ethanlefebv/S4H2021-Scarus/Mechanical_Components/ASSY_SCARUS/ASSY_ROBOT/ARM_SEGMENT_1.SLDPRT

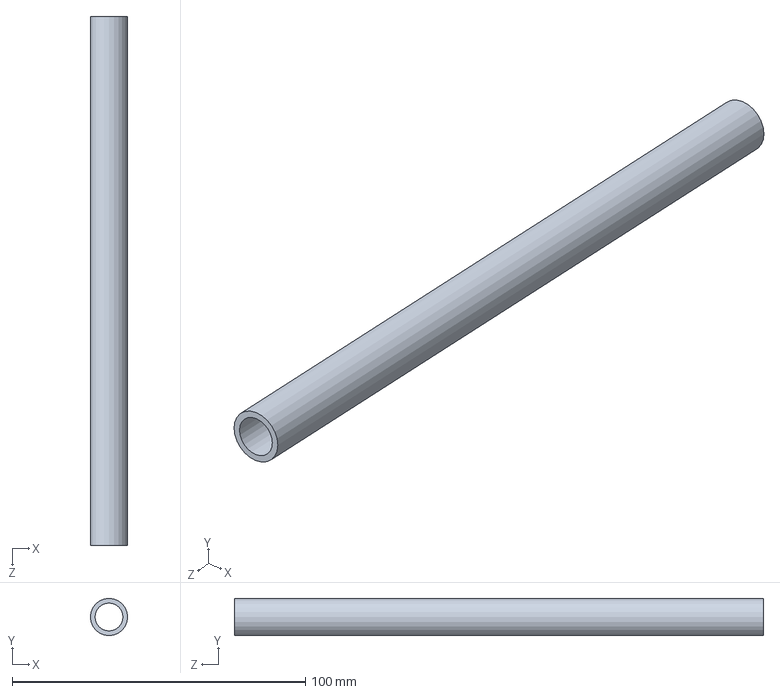
[picture p18: CAD file, 2021-04-16]
Mechanical_Components/ASSY_SCARUS/ASSY_ROBOT/ARM_SEGMENT_1.SLDPRT
12.7 x 12.7 x 180.4 mm
