ethanlefebv/S4H2021-Scarus/Mechanical_Components/ASSY_SCARUS/ASSY_ROBOT/ASSY_GRIPPER_QUICK_CONNECT/ASSY_FAN/Cooler Blades.SLDPRT

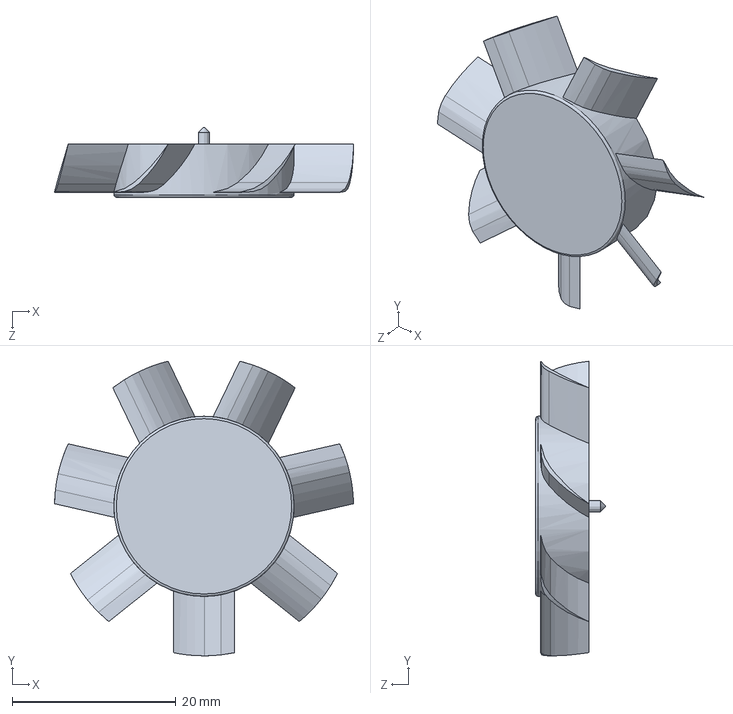
[picture p19: CAD file, 2021-04-16]
Mechanical_Components/ASSY_SCARUS/ASSY_ROBOT/ASSY_GRIPPER_QUICK_CONNECT/ASSY_FAN/Cooler Blades.SLDPRT
36.5 x 36.0 x 8.50 mm
