ethanlefebv/S4H2021-Scarus/Mechanical_Components/ASSY_SCARUS/ASSY_ROBOT/ASSY_GRIPPER_QUICK_CONNECT/ASSY_SOLENOID/SOLENOID_SLIDER.SLDPRT

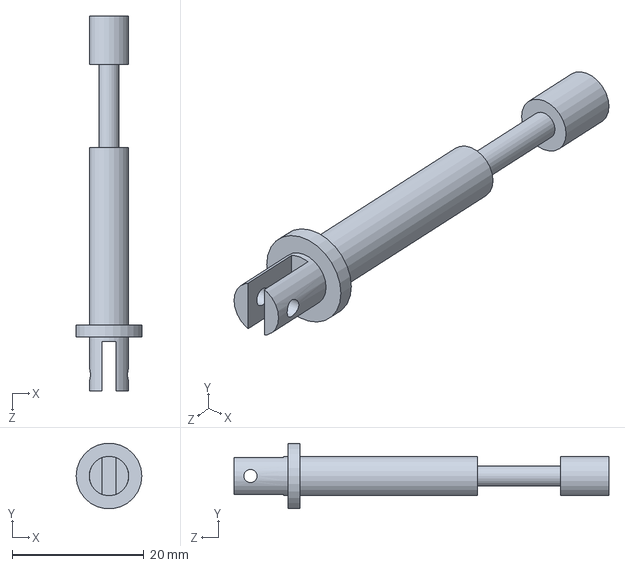
[picture p20: CAD file, 2021-04-16]
Mechanical_Components/ASSY_SCARUS/ASSY_ROBOT/ASSY_GRIPPER_QUICK_CONNECT/ASSY_SOLENOID/SOLENOID_SLIDER.SLDPRT
10.0 x 9.93 x 57.0 mm
