ethanlefebv/S4H2021-Scarus/Mechanical_Components/ASSY_SCARUS/ASSY_SLIDE/SLIDE.SLDPRT

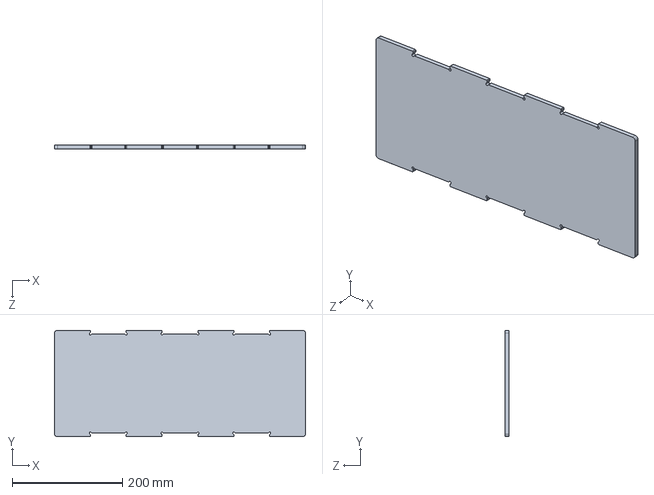
[picture p22: CAD file, 2021-04-16]
Mechanical_Components/ASSY_SCARUS/ASSY_SLIDE/SLIDE.SLDPRT
455.0 x 192.7 x 6.35 mm
