ethanlefebv/S4H2021-Scarus/Mechanical_Components/DXF/ROBOT_BASE/RBASE_BASE.DXF

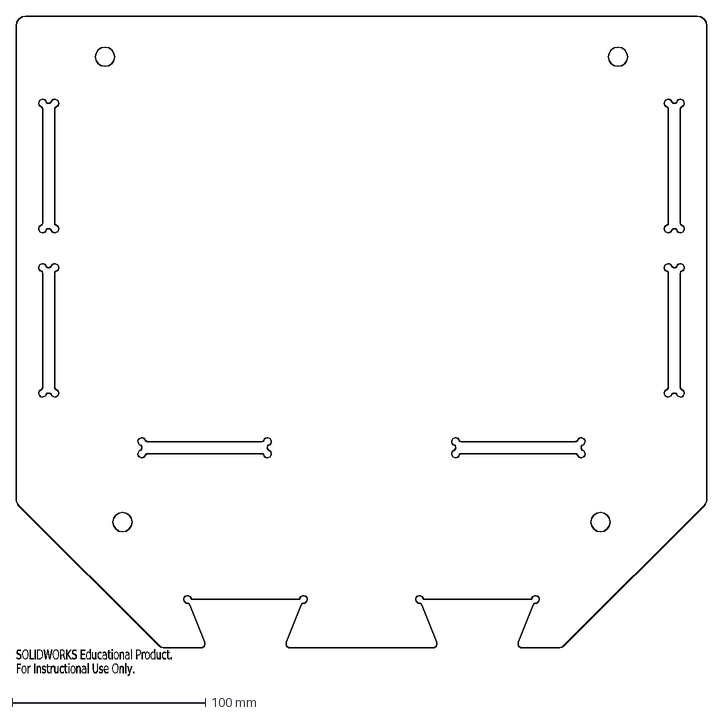
[picture p23: CAD file, 2021-04-16]
Mechanical_Components/DXF/ROBOT_BASE/RBASE_BASE.DXF
SOLIDWORKS Educational Product.
For Instructional Use Only.
