ethanlefebv/S4H2021-Scarus/Mechanical_Components/MOTOR_STAND/MOTOR_STAND_HIGH.SLDPRT

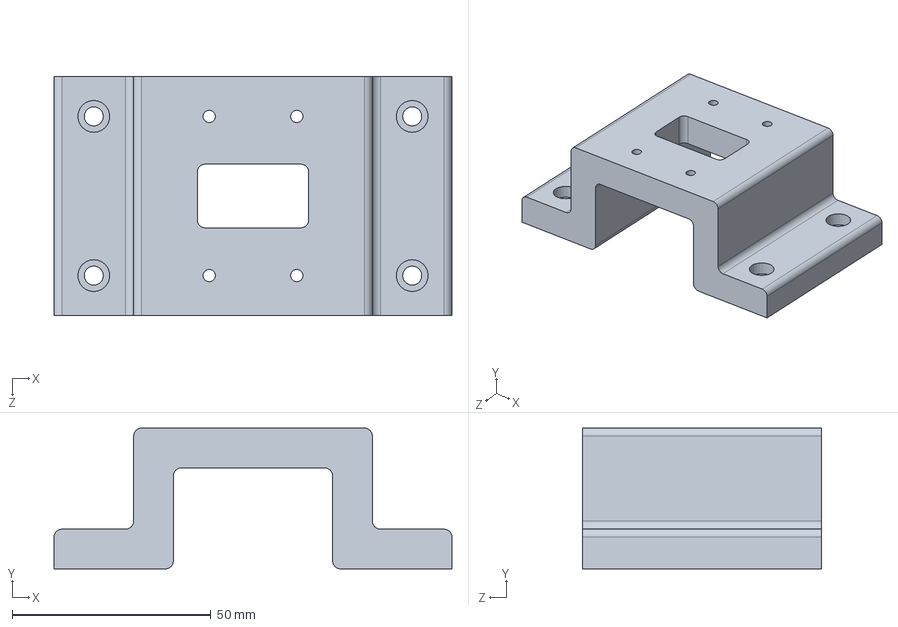
[picture p25: CAD file, 2021-04-16]
Mechanical_Components/MOTOR_STAND/MOTOR_STAND_HIGH.SLDPRT
100.0 x 35.4 x 60.0 mm
