ethanlefebv/S4H2021-Scarus/Mechanical_Components/STL/Gripper/LIFTING_SOLENOID_HOLDER.STL

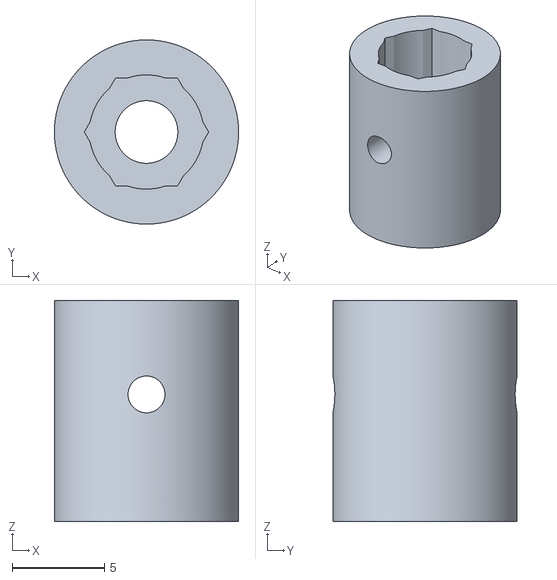
[picture p26: CAD file, 2021-04-16]
Mechanical_Components/STL/Gripper/LIFTING_SOLENOID_HOLDER.STL
10.0 x 10.0 x 12.0
