ethanlefebv/S4H2021-Scarus/Mechanical_Components/STL/PLA_BUCKET.STL

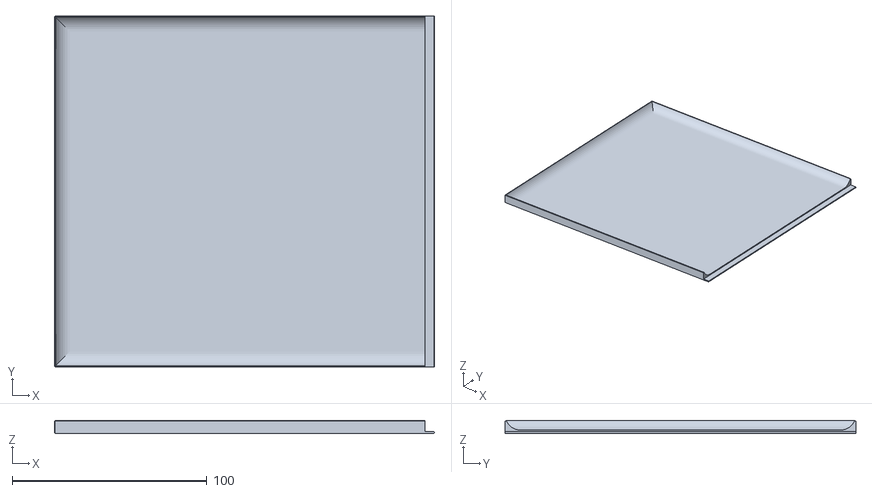
[picture p27: CAD file, 2021-02-24]
Mechanical_Components/STL/PLA_BUCKET.STL
195.0 x 180.0 x 6.42
