ethanlefebv/S4H2021-Scarus/Mechanical_Components/STL/Robot/Motors/BEARING_HOUSING.STL

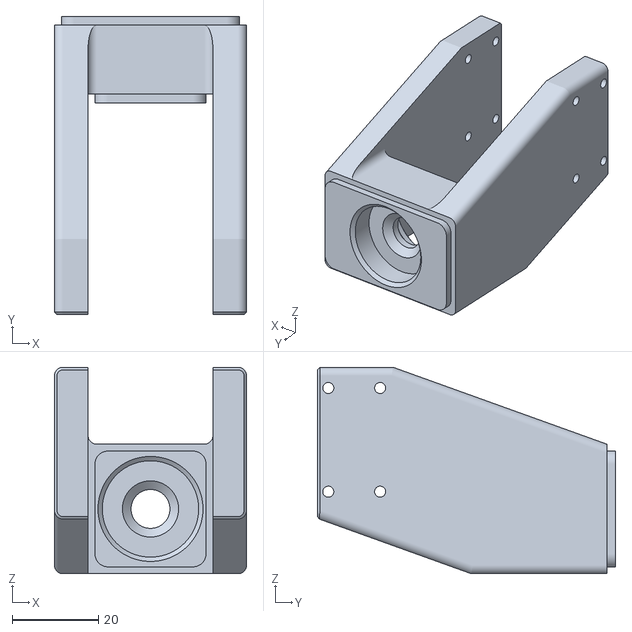
[picture p28: CAD file, 2021-04-16]
Mechanical_Components/STL/Robot/Motors/BEARING_HOUSING.STL
44.5 x 69.0 x 47.8
