ethanlefebv/S4H2021-Scarus/Mechanical_Components/ASSY_GRIPPER/SOLENOID_FIXTURE.SLDPRT

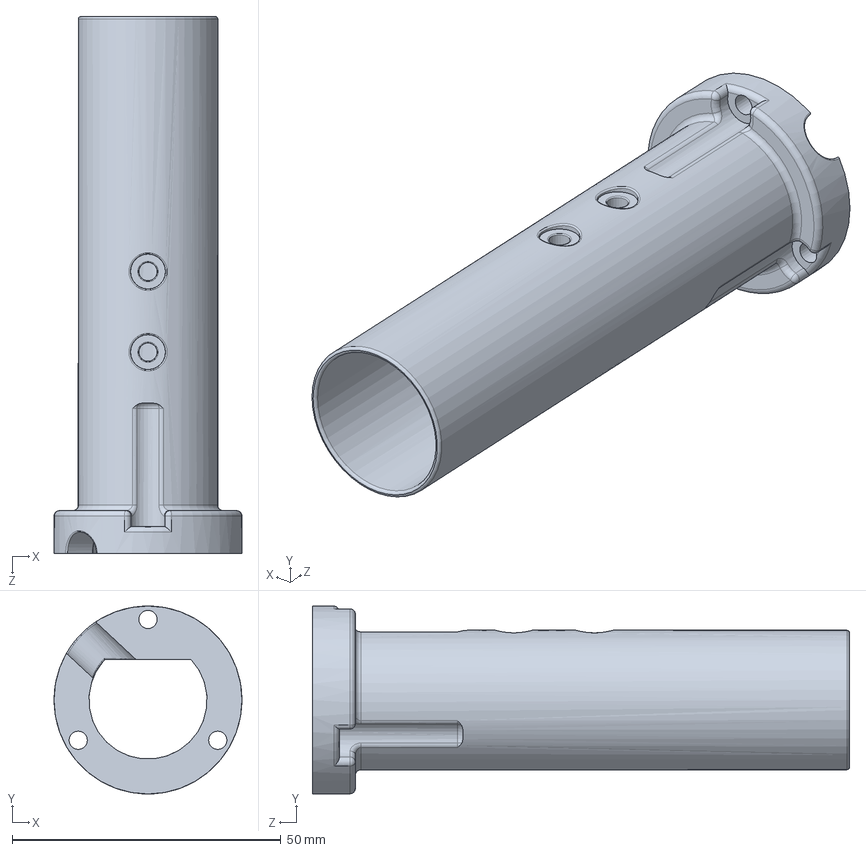
[picture p29: CAD file, 2021-04-16]
Mechanical_Components/ASSY_GRIPPER/SOLENOID_FIXTURE.SLDPRT
35.0 x 35.0 x 100.0 mm
