ethanlefebv/S4H2021-Scarus/Mechanical_Components/ASSY_SCARUS/ASSY_ROBOT/ASSY_GRIPPER_QUICK_CONNECT/ACTIONNEUR.SLDPRT

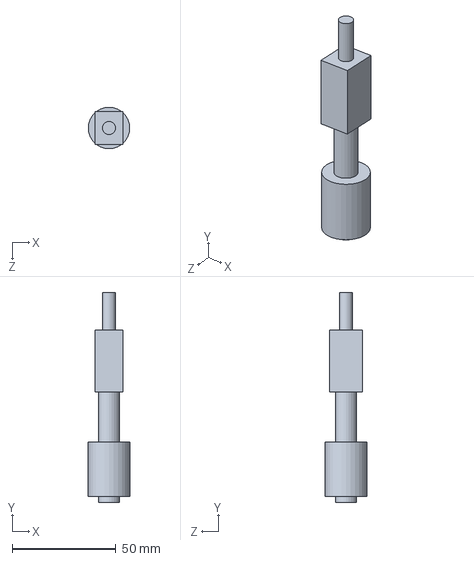
[picture p30: CAD file, 2021-04-16]
Mechanical_Components/ASSY_SCARUS/ASSY_ROBOT/ASSY_GRIPPER_QUICK_CONNECT/ACTIONNEUR.SLDPRT
20.0 x 101.2 x 20.0 mm
