ethanlefebv/S4H2021-Scarus/Mechanical_Components/ASSY_SCARUS/ASSY_ROBOT/ASSY_GRIPPER_QUICK_CONNECT/ASSY_FAN/Cooler 40x40x10 body.SLDPRT

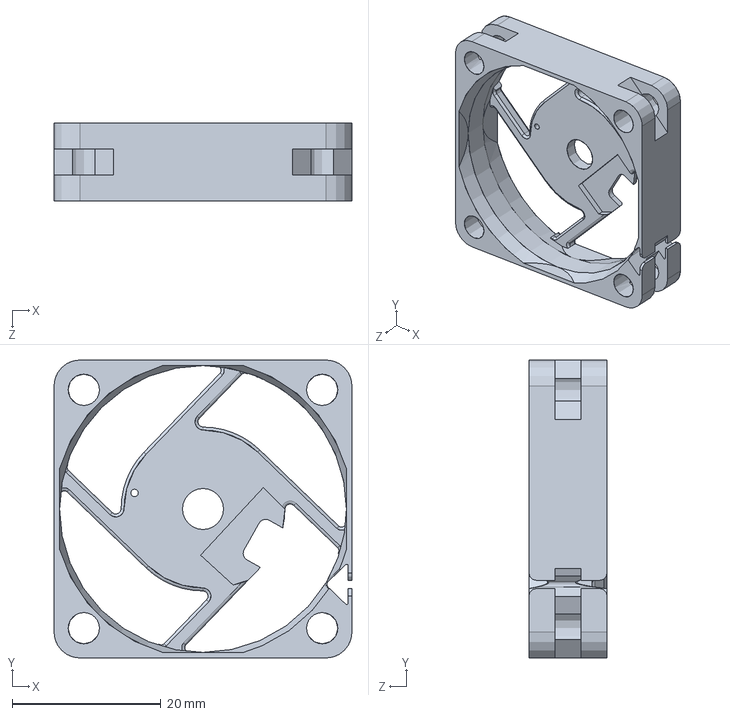
[picture p31: CAD file, 2021-04-16]
Mechanical_Components/ASSY_SCARUS/ASSY_ROBOT/ASSY_GRIPPER_QUICK_CONNECT/ASSY_FAN/Cooler 40x40x10 body.SLDPRT
40.0 x 40.0 x 10.5 mm
