ethanlefebv/S4H2021-Scarus/Mechanical_Components/ASSY_SCARUS/ASSY_ROBOT/ASSY_JOINTS/JOINT_STD.SLDPRT

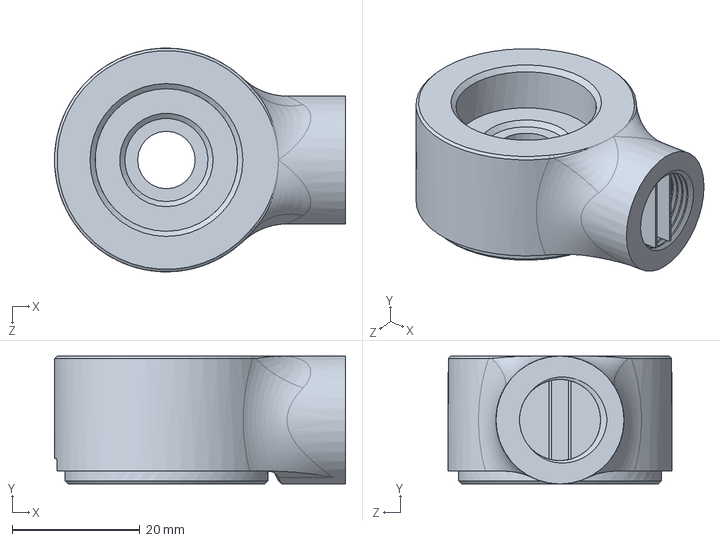
[picture p32: CAD file, 2021-04-16]
Mechanical_Components/ASSY_SCARUS/ASSY_ROBOT/ASSY_JOINTS/JOINT_STD.SLDPRT
45.5 x 20.0 x 35.0 mm
