ethanlefebv/S4H2021-Scarus/Mechanical_Components/ASSY_SCARUS/ASSY_ROBOT/BEARING_HOUSING.SLDPRT

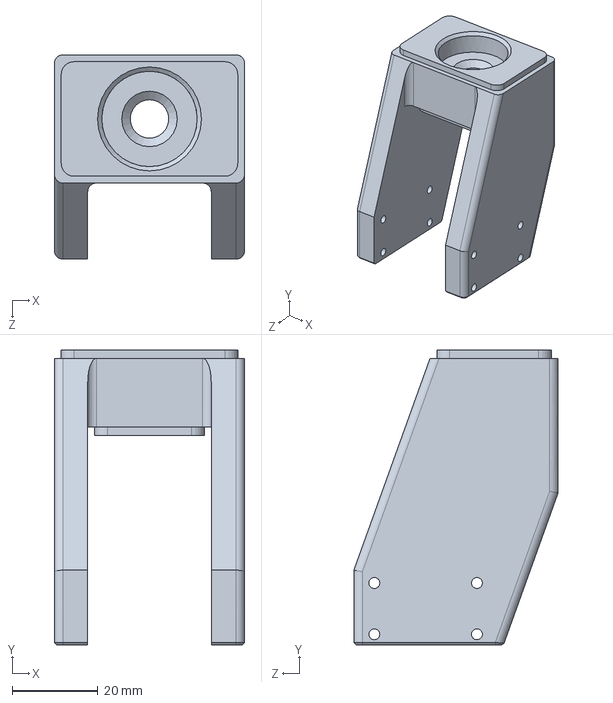
[picture p33: CAD file, 2021-04-16]
Mechanical_Components/ASSY_SCARUS/ASSY_ROBOT/BEARING_HOUSING.SLDPRT
44.5 x 69.0 x 47.8 mm
