ethanlefebv/S4H2021-Scarus/Mechanical_Components/DXF/SLIDE/SLIDE_BASE.DXF

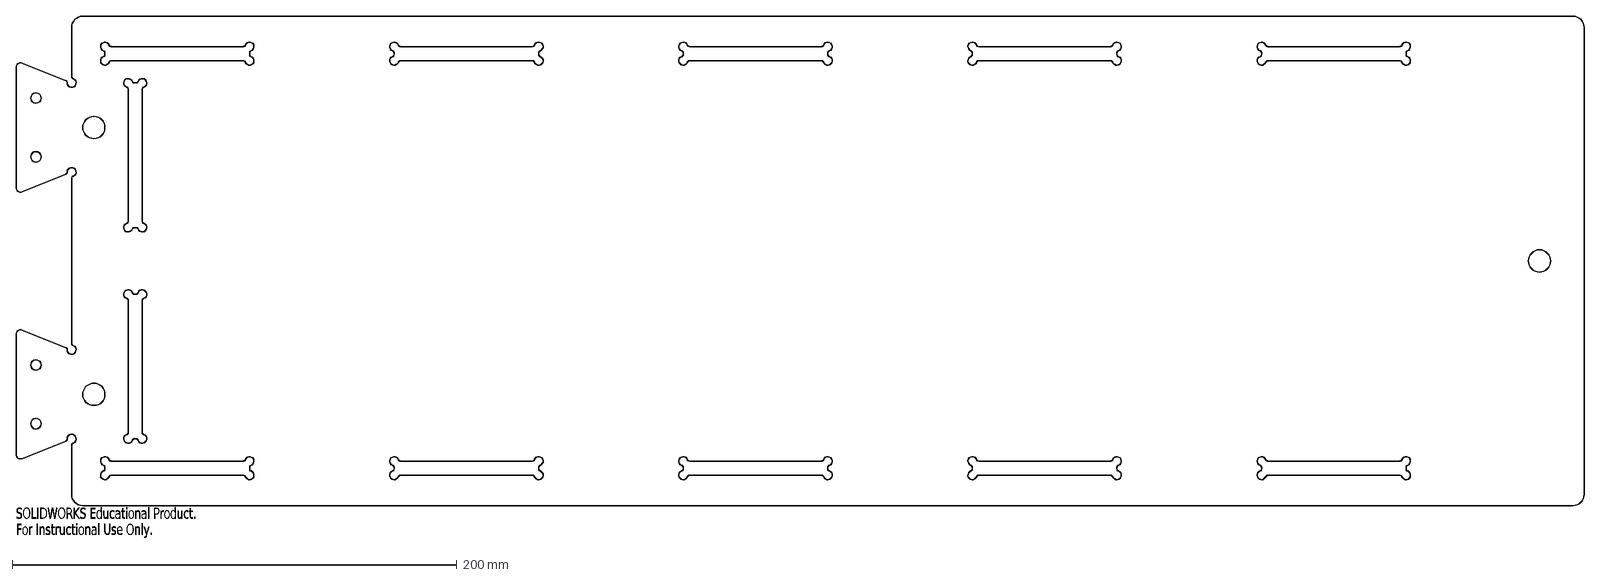
[picture p35: CAD file, 2021-04-16]
Mechanical_Components/DXF/SLIDE/SLIDE_BASE.DXF
SOLIDWORKS Educational Product.
For Instructional Use Only.
