ethanlefebv/S4H2021-Scarus/Mechanical_Components/MOTOR_STAND/MOTOR_STAND_BOT_WOOD.SLDPRT

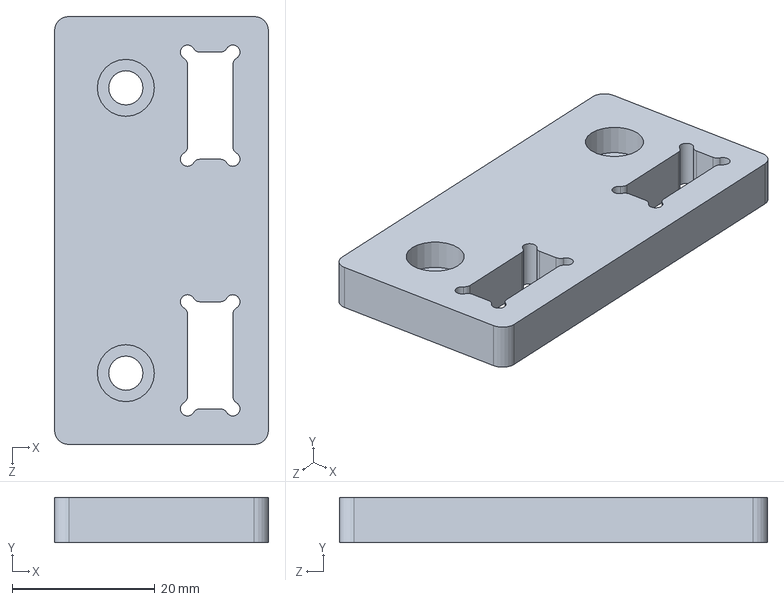
[picture p36: CAD file, 2021-04-16]
Mechanical_Components/MOTOR_STAND/MOTOR_STAND_BOT_WOOD.SLDPRT
30.0 x 6.35 x 60.0 mm
