ethanlefebv/S4H2021-Scarus/Mechanical_Components/STL/Gripper/SOLENOID_DOOR.STL

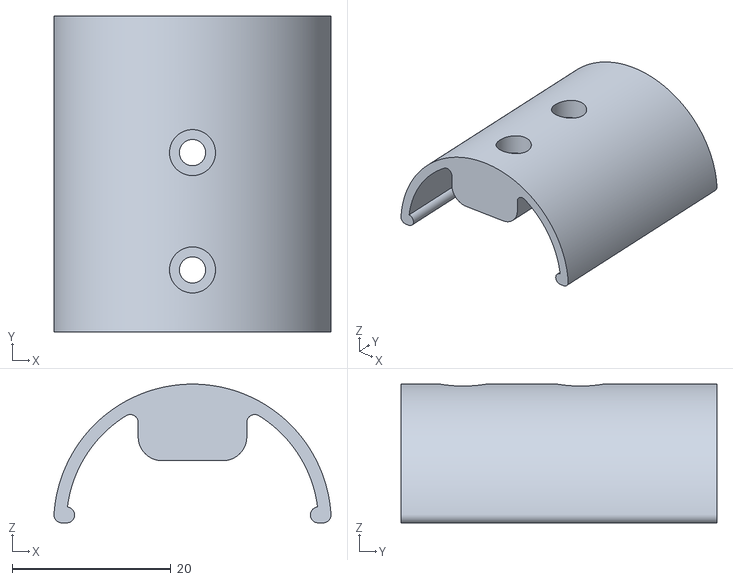
[picture p37: CAD file, 2021-04-16]
Mechanical_Components/STL/Gripper/SOLENOID_DOOR.STL
34.9 x 39.8 x 17.5
