ethanlefebv/S4H2021-Scarus/Mechanical_Components/STL/Robot/Joints/SPACER.STL

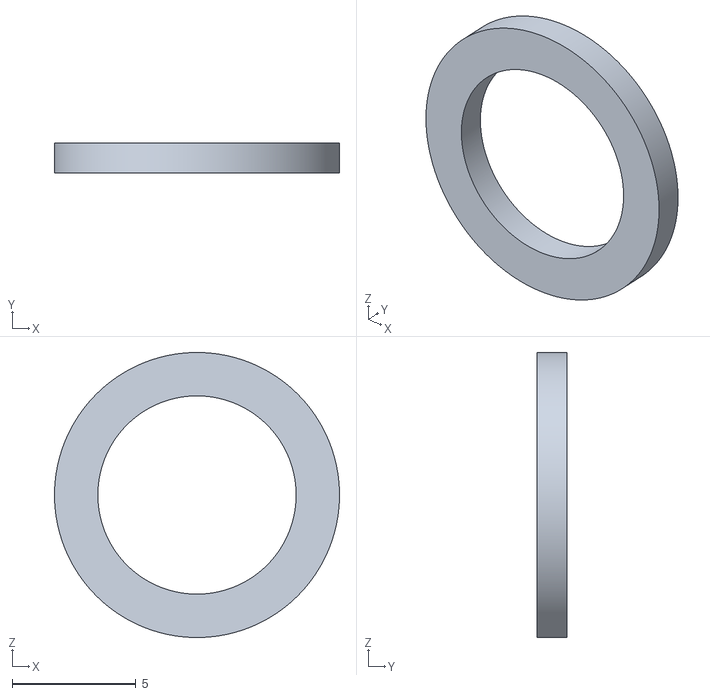
[picture p38: CAD file, 2021-04-16]
Mechanical_Components/STL/Robot/Joints/SPACER.STL
11.5 x 1.20 x 11.5
