ethanlefebv/S4H2021-Scarus/Mechanical_Components/STL/Robot/Motors/MOTOR_STAND_HIGH.STL

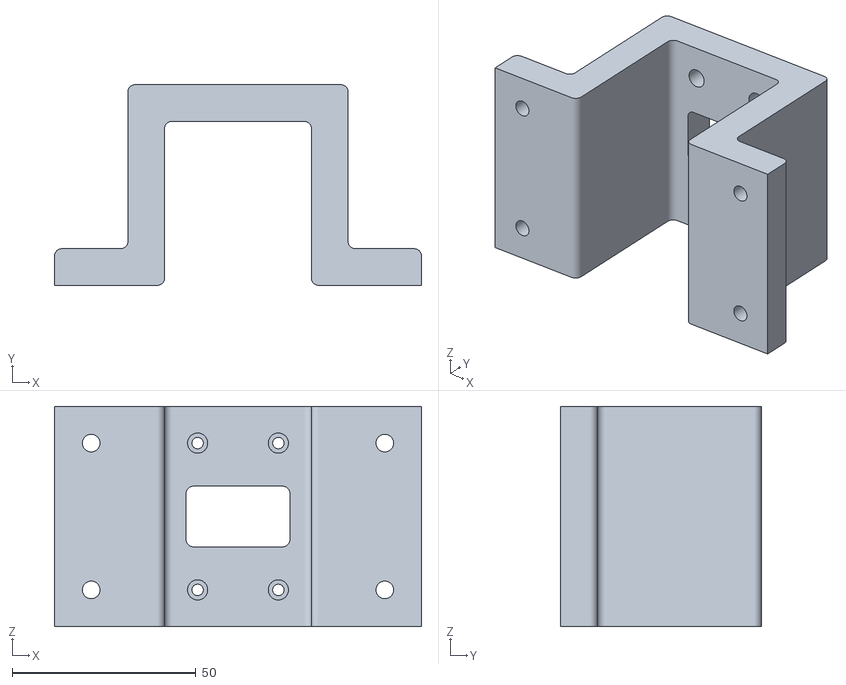
[picture p39: CAD file, 2021-04-16]
Mechanical_Components/STL/Robot/Motors/MOTOR_STAND_HIGH.STL
100.0 x 54.7 x 60.0
