ethanlefebv/S4H2021-Scarus/Mechanical_Components/ASSY_SCARUS/ASSY_ROBOT/ASSY_GRIPPER_QUICK_CONNECT/ASSY_FAN/Sticker SUNON.SLDPRT

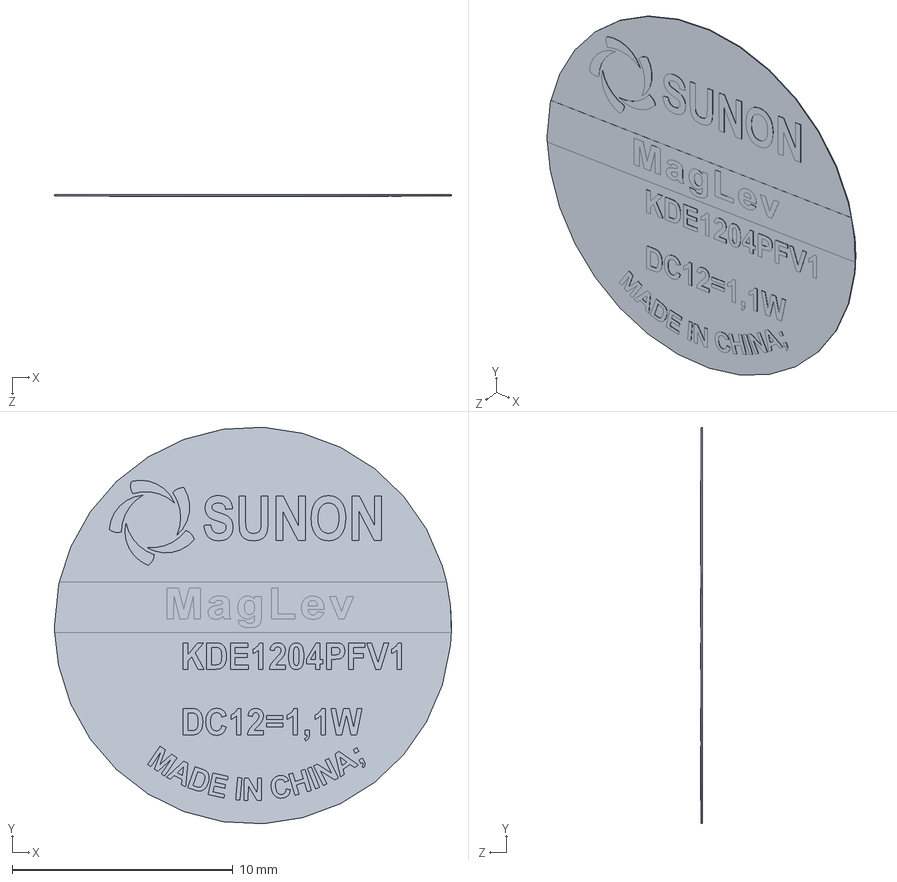
[picture p40: CAD file, 2021-04-16]
Mechanical_Components/ASSY_SCARUS/ASSY_ROBOT/ASSY_GRIPPER_QUICK_CONNECT/ASSY_FAN/Sticker SUNON.SLDPRT
18.0 x 18.0 x 0.07 mm
