ethanlefebv/S4H2021-Scarus/Mechanical_Components/ASSY_SCARUS/ASSY_ROBOT/ASSY_JOINTS/SPACER.SLDPRT

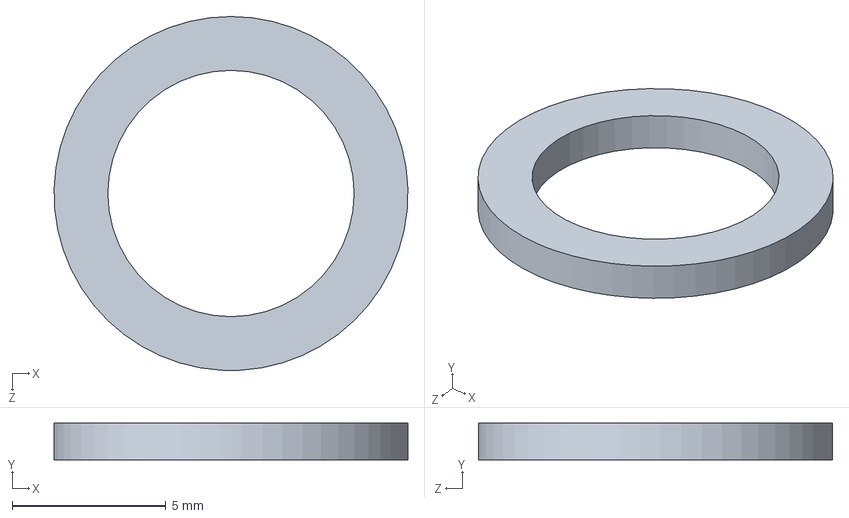
[picture p42: CAD file, 2021-04-16]
Mechanical_Components/ASSY_SCARUS/ASSY_ROBOT/ASSY_JOINTS/SPACER.SLDPRT
11.5 x 1.20 x 11.5 mm
