ethanlefebv/S4H2021-Scarus/Mechanical_Components/ASSY_SCARUS/ASSY_SLIDE/CAM.SLDPRT

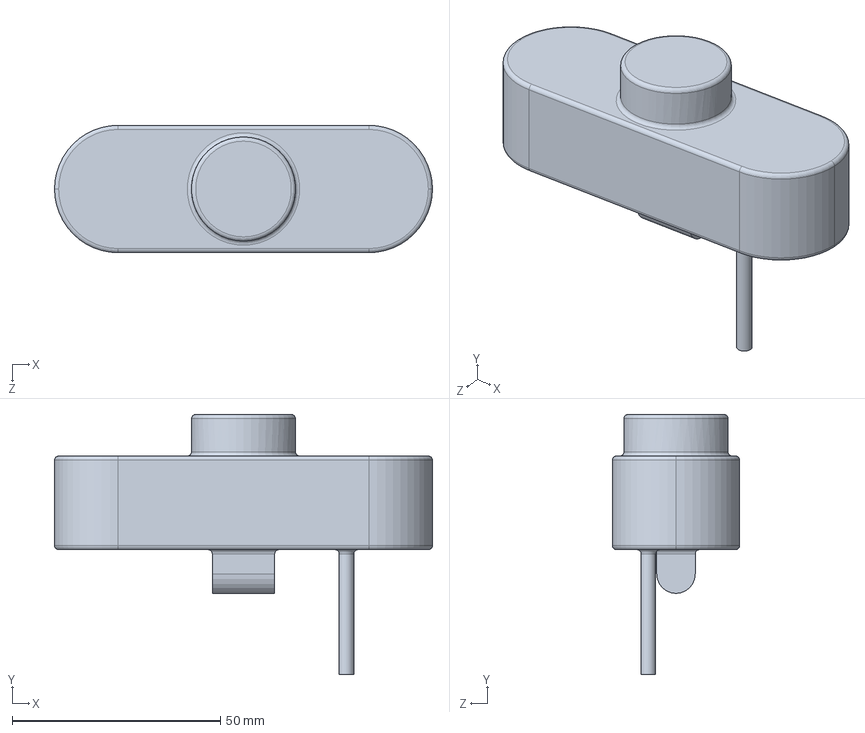
[picture p43: CAD file, 2021-04-16]
Mechanical_Components/ASSY_SCARUS/ASSY_SLIDE/CAM.SLDPRT
90.8 x 62.5 x 30.6 mm
