ethanlefebv/S4H2021-Scarus/Mechanical_Components/DXF/ROBOT_BASE/RBASE_TOP.DXF

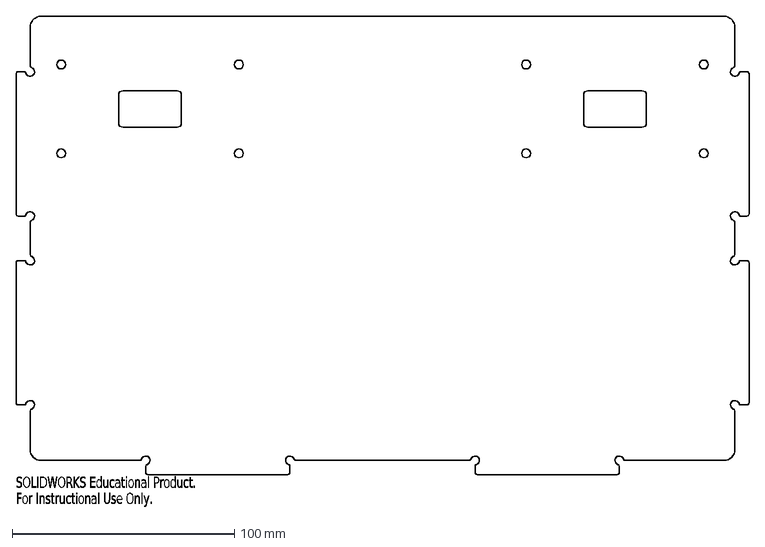
[picture p44: CAD file, 2021-04-16]
Mechanical_Components/DXF/ROBOT_BASE/RBASE_TOP.DXF
SOLIDWORKS Educational Product.
For Instructional Use Only.
