ethanlefebv/S4H2021-Scarus/Mechanical_Components/MOTOR_STAND/MOTOR_STAND_HIGH_SIDE_WOOD.SLDPRT

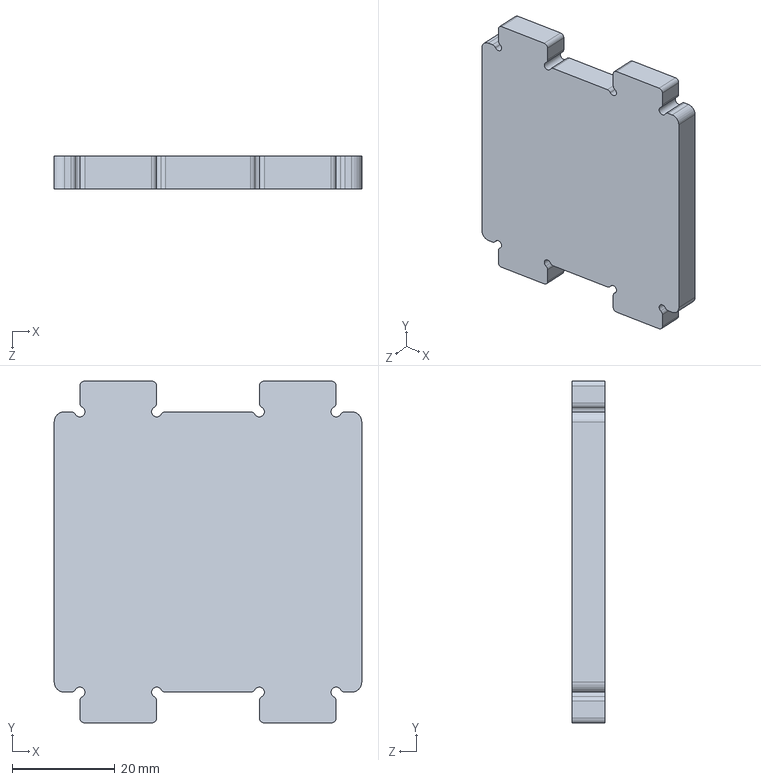
[picture p46: CAD file, 2021-04-16]
Mechanical_Components/MOTOR_STAND/MOTOR_STAND_HIGH_SIDE_WOOD.SLDPRT
60.0 x 66.7 x 6.35 mm
