ethanlefebv/S4H2021-Scarus/Mechanical_Components/STL/Robot/Motors/MOTOR_STAND.STL

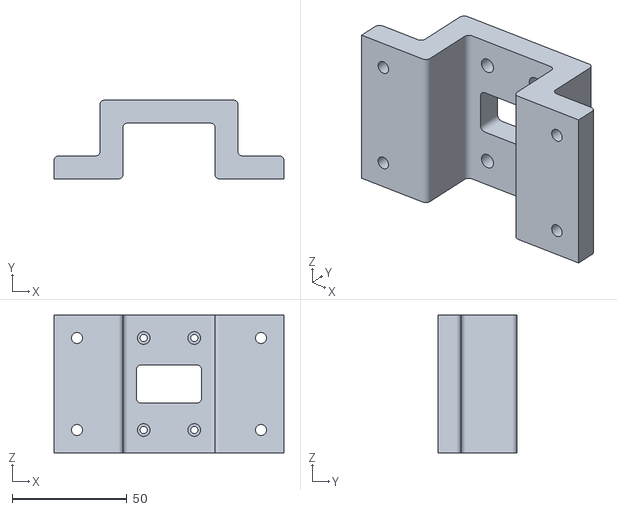
[picture p47: CAD file, 2021-04-16]
Mechanical_Components/STL/Robot/Motors/MOTOR_STAND.STL
100.0 x 34.3 x 60.0
