ethanlefebv/S4H2021-Scarus/Mechanical_Components/ASSY_SCARUS/ASSY_ROBOT/ASSY_GRIPPER_QUICK_CONNECT/ASSY_FAN/Cooler pcb.SLDPRT

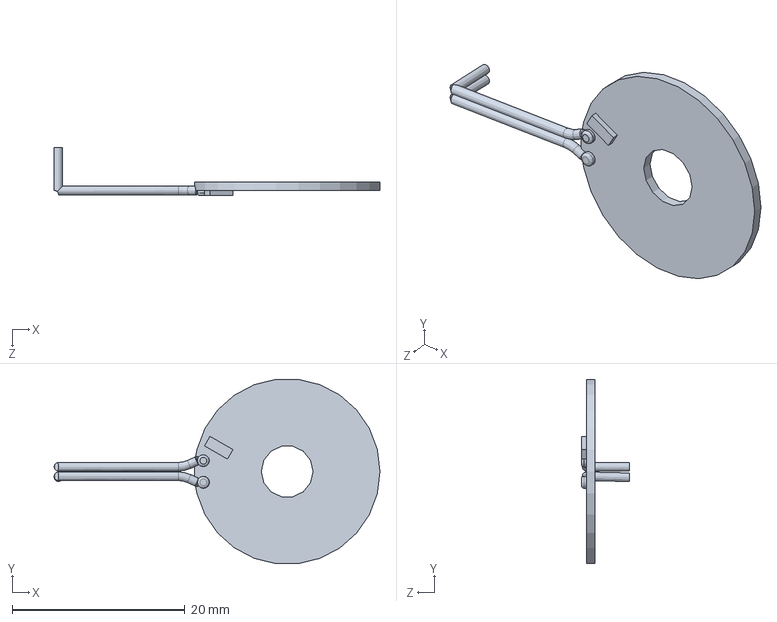
[picture p48: CAD file, 2021-04-16]
Mechanical_Components/ASSY_SCARUS/ASSY_ROBOT/ASSY_GRIPPER_QUICK_CONNECT/ASSY_FAN/Cooler pcb.SLDPRT
37.8 x 21.3 x 5.61 mm
