ethanlefebv/S4H2021-Scarus/Mechanical_Components/ASSY_SCARUS/ASSY_ROBOT/ASSY_JOINTS/JOINT_STD_V2.SLDPRT

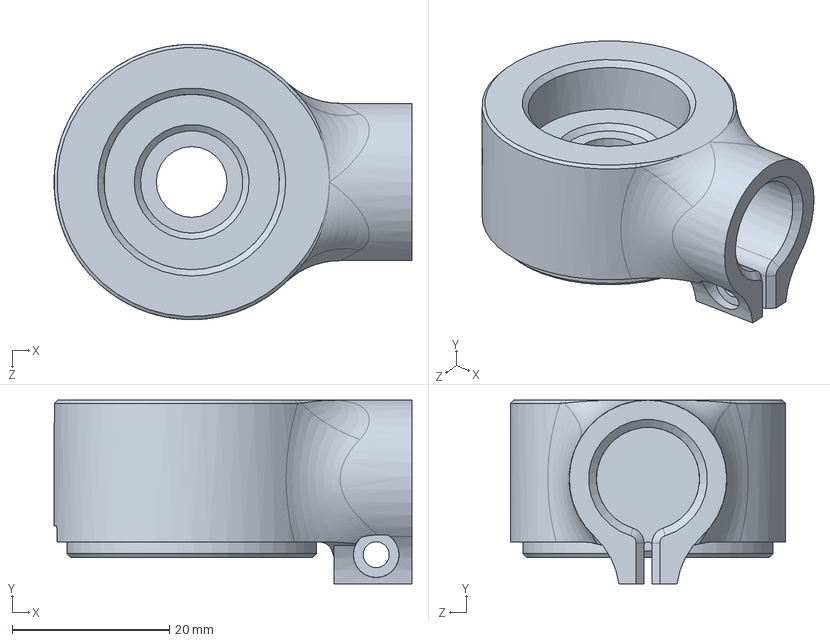
[picture p49: CAD file, 2021-04-16]
Mechanical_Components/ASSY_SCARUS/ASSY_ROBOT/ASSY_JOINTS/JOINT_STD_V2.SLDPRT
45.5 x 23.3 x 35.0 mm
