ethanlefebv/S4H2021-Scarus/Mechanical_Components/DXF/ROBOT_BASE/RBASE_SLIDER_SUPPORT.DXF

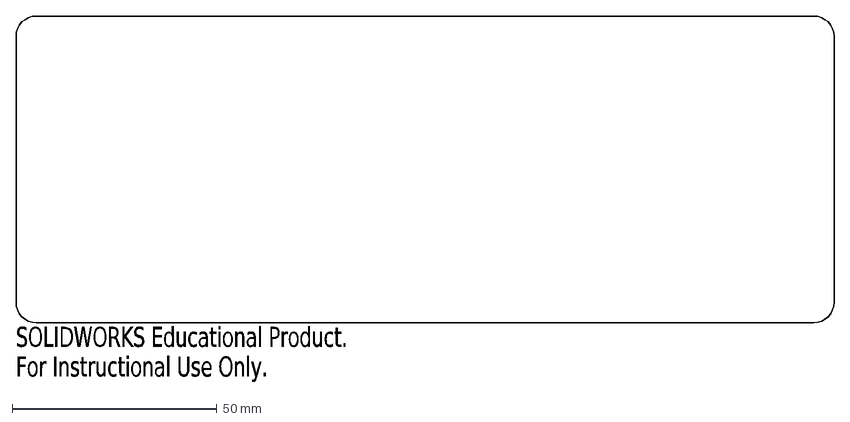
[picture p50: CAD file, 2021-04-16]
Mechanical_Components/DXF/ROBOT_BASE/RBASE_SLIDER_SUPPORT.DXF
SOLIDWORKS Educational Product.
For Instructional Use Only.
