ethanlefebv/S4H2021-Scarus/Mechanical_Components/DXF/SLIDE/SLIDE_BUCKET.DXF

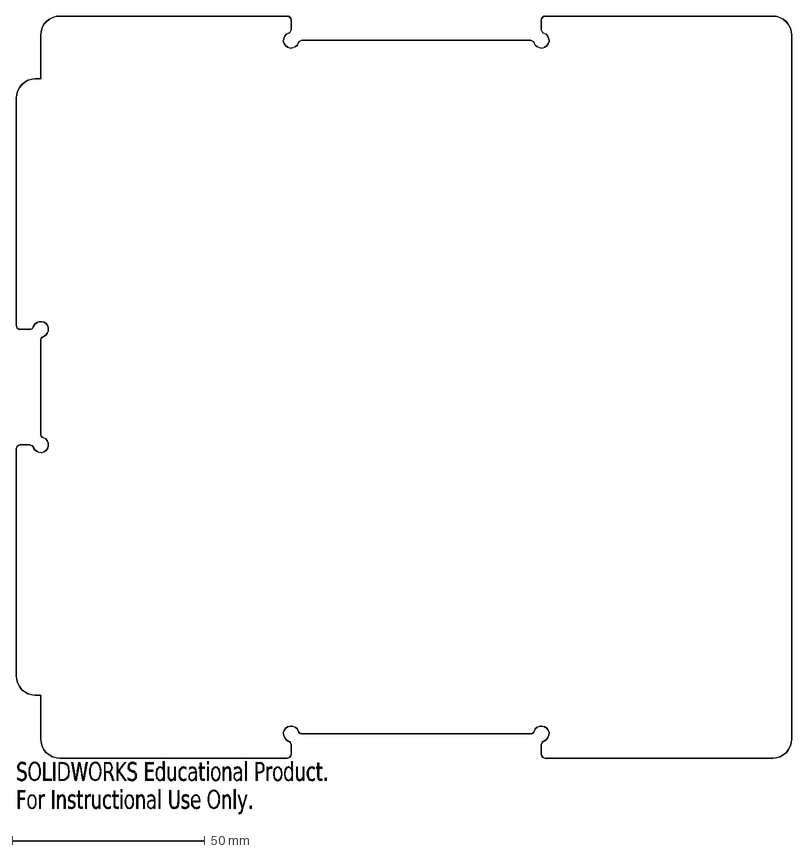
[picture p51: CAD file, 2021-04-16]
Mechanical_Components/DXF/SLIDE/SLIDE_BUCKET.DXF
SOLIDWORKS Educational Product.
For Instructional Use Only.
