ethanlefebv/S4H2021-Scarus/Mechanical_Components/MOTOR_STAND/MOTOR_STAND_SIDE_WOOD.SLDPRT

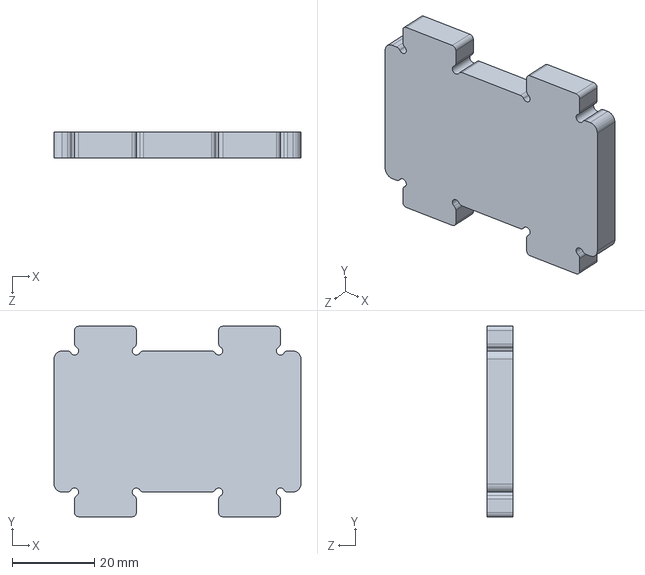
[picture p52: CAD file, 2021-04-16]
Mechanical_Components/MOTOR_STAND/MOTOR_STAND_SIDE_WOOD.SLDPRT
60.0 x 46.3 x 6.35 mm
