ethanlefebv/S4H2021-Scarus/Mechanical_Components/ASSY_SCARUS/ASSY_SLIDE/SIDE_CAM_SUPPORT.SLDPRT

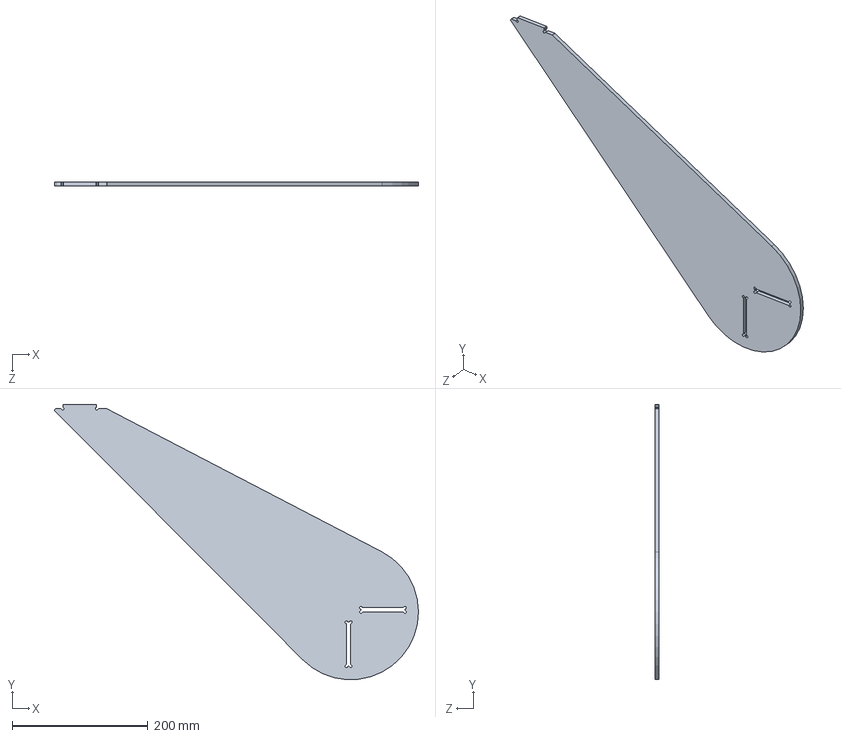
[picture p55: CAD file, 2021-04-16]
Mechanical_Components/ASSY_SCARUS/ASSY_SLIDE/SIDE_CAM_SUPPORT.SLDPRT
537.2 x 406.2 x 6.35 mm
