ethanlefebv/S4H2021-Scarus/Mechanical_Components/MOTOR_STAND/MOTOR_STAND_TOP_WOOD.SLDPRT

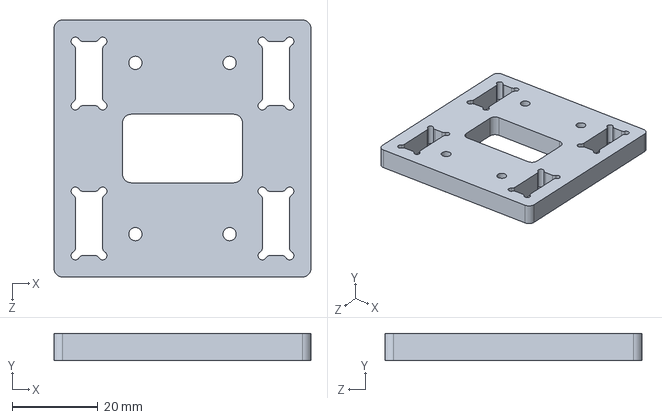
[picture p58: CAD file, 2021-04-16]
Mechanical_Components/MOTOR_STAND/MOTOR_STAND_TOP_WOOD.SLDPRT
60.0 x 6.35 x 60.0 mm
