ethanlefebv/S4H2021-Scarus/Mechanical_Components/STL/Robot/Motors/CAP_BEARING_TOP.STL

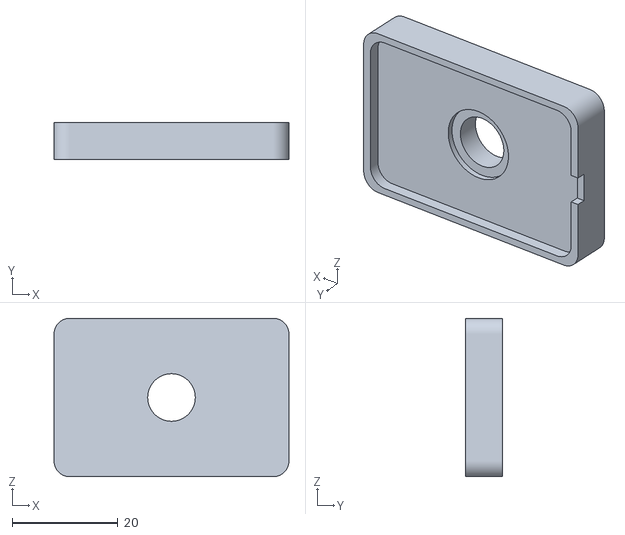
[picture p59: CAD file, 2021-04-16]
Mechanical_Components/STL/Robot/Motors/CAP_BEARING_TOP.STL
44.5 x 7.00 x 30.0
