ethanlefebv/S4H2021-Scarus/Mechanical_Components/ASSY_SCARUS/ASSY_ROBOT/ASSY_GRIPPER_QUICK_CONNECT/SOLENOID_COVER_V2.SLDPRT

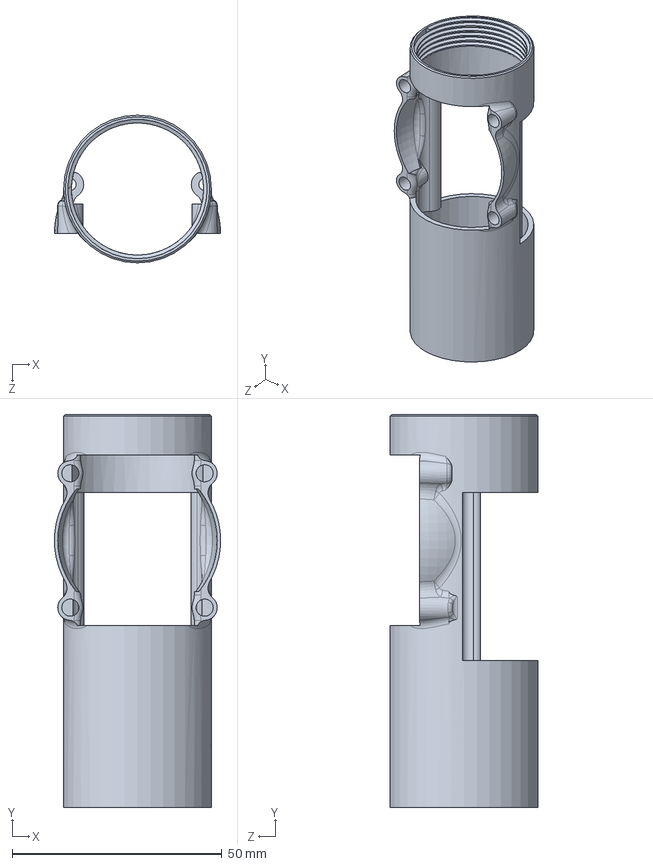
[picture p61: CAD file, 2021-04-16]
Mechanical_Components/ASSY_SCARUS/ASSY_ROBOT/ASSY_GRIPPER_QUICK_CONNECT/SOLENOID_COVER_V2.SLDPRT
39.6 x 93.6 x 35.2 mm
