ethanlefebv/S4H2021-Scarus/Mechanical_Components/ASSY_SCARUS/ASSY_SLIDE/SUPPORT_SLIDING_BOARD.SLDPRT

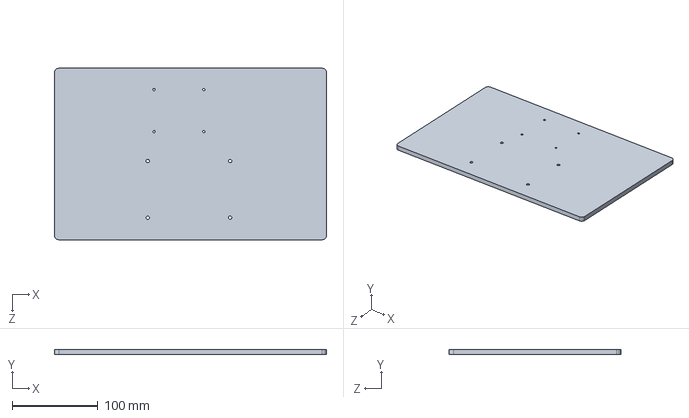
[picture p62: CAD file, 2021-04-16]
Mechanical_Components/ASSY_SCARUS/ASSY_SLIDE/SUPPORT_SLIDING_BOARD.SLDPRT
317.0 x 6.35 x 200.0 mm
