ethanlefebv/S4H2021-Scarus/Mechanical_Components/DXF/ROBOT_BASE/RBASE_SIDE_WALL.DXF

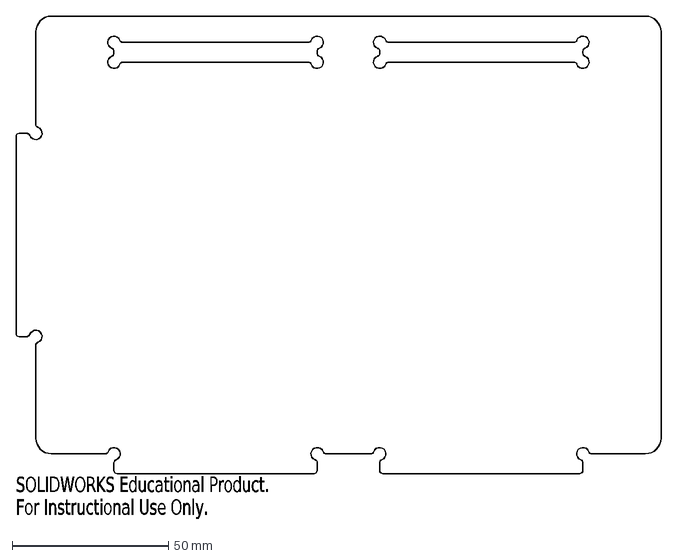
[picture p63: CAD file, 2021-04-16]
Mechanical_Components/DXF/ROBOT_BASE/RBASE_SIDE_WALL.DXF
SOLIDWORKS Educational Product.
For Instructional Use Only.
