ethanlefebv/S4H2021-Scarus/Mechanical_Components/DXF/SLIDE/SLIDE_BED.DXF

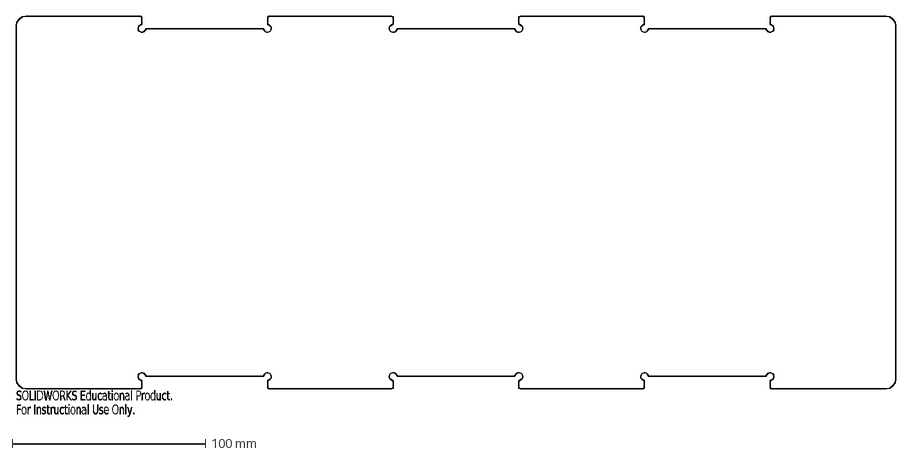
[picture p64: CAD file, 2021-04-16]
Mechanical_Components/DXF/SLIDE/SLIDE_BED.DXF
SOLIDWORKS Educational Product.
For Instructional Use Only.
