ethanlefebv/S4H2021-Scarus/Mechanical_Components/MOTOR_STAND/MOTOR_STAND.SLDPRT

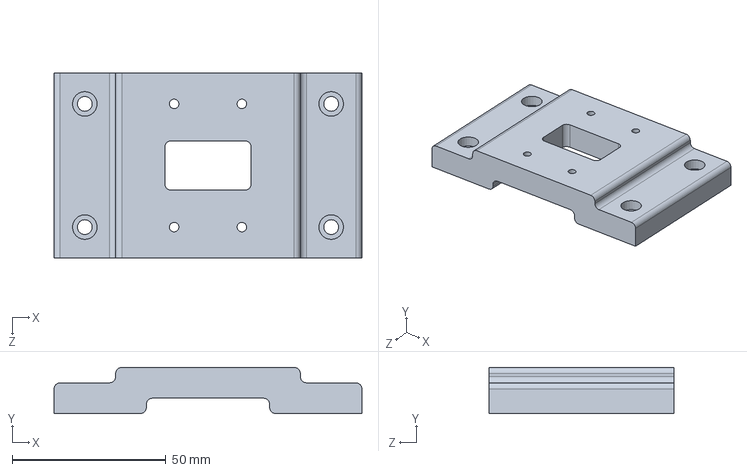
[picture p65: CAD file, 2021-04-16]
Mechanical_Components/MOTOR_STAND/MOTOR_STAND.SLDPRT
100.0 x 15.0 x 60.0 mm
