ethanlefebv/S4H2021-Scarus/Mechanical_Components/ASSY_SCARUS/ASSY_SLIDE/LOCK_CAM_SUPPORT.SLDPRT

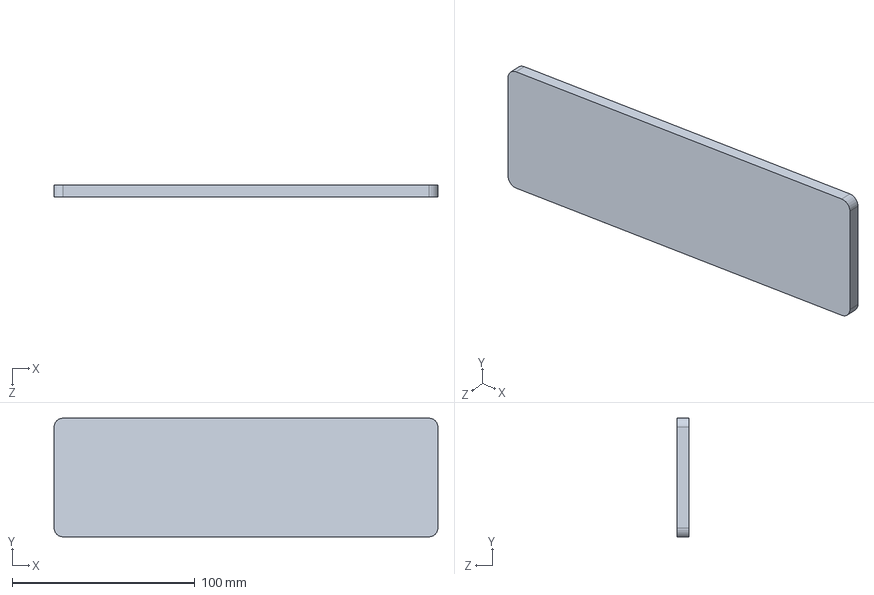
[picture p66: CAD file, 2021-04-16]
Mechanical_Components/ASSY_SCARUS/ASSY_SLIDE/LOCK_CAM_SUPPORT.SLDPRT
210.0 x 65.0 x 6.35 mm
