ethanlefebv/S4H2021-Scarus/Mechanical_Components/DXF/SLIDE/SLIDE_DOVETAIL_SPACER.DXF

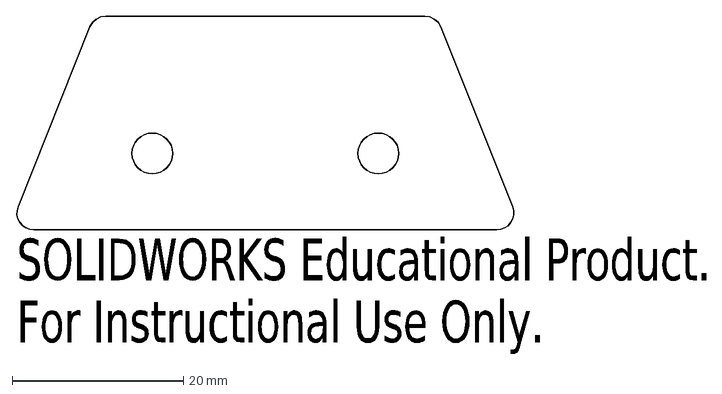
[picture p67: CAD file, 2021-04-16]
Mechanical_Components/DXF/SLIDE/SLIDE_DOVETAIL_SPACER.DXF
SOLIDWORKS Educational Product.
For Instructional Use Only.
