ethanlefebv/S4H2021-Scarus/Mechanical_Components/ASSY_SCARUS/ASSY_SLIDE/SUPPORT_BASE.SLDPRT

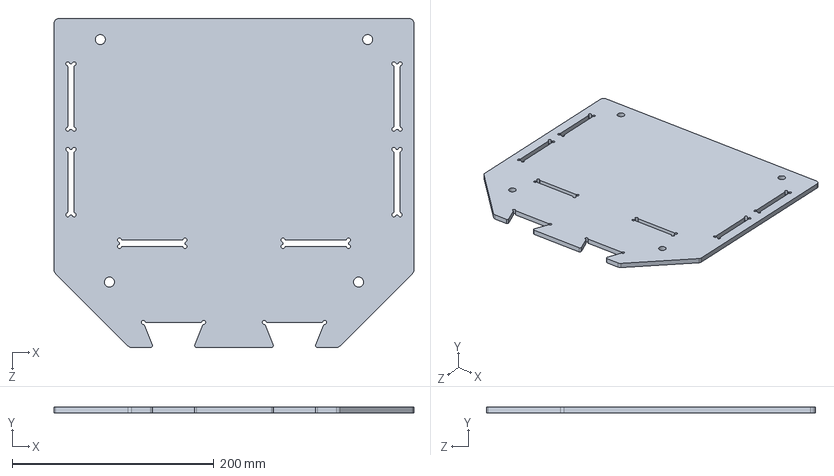
[picture p68: CAD file, 2021-04-16]
Mechanical_Components/ASSY_SCARUS/ASSY_SLIDE/SUPPORT_BASE.SLDPRT
357.3 x 6.35 x 326.7 mm
