ethanlefebv/S4H2021-Scarus/Mechanical_Components/ASSY_SCARUS/ASSY_ROBOT/DYNAMIXEL_COUPLING.sldprt

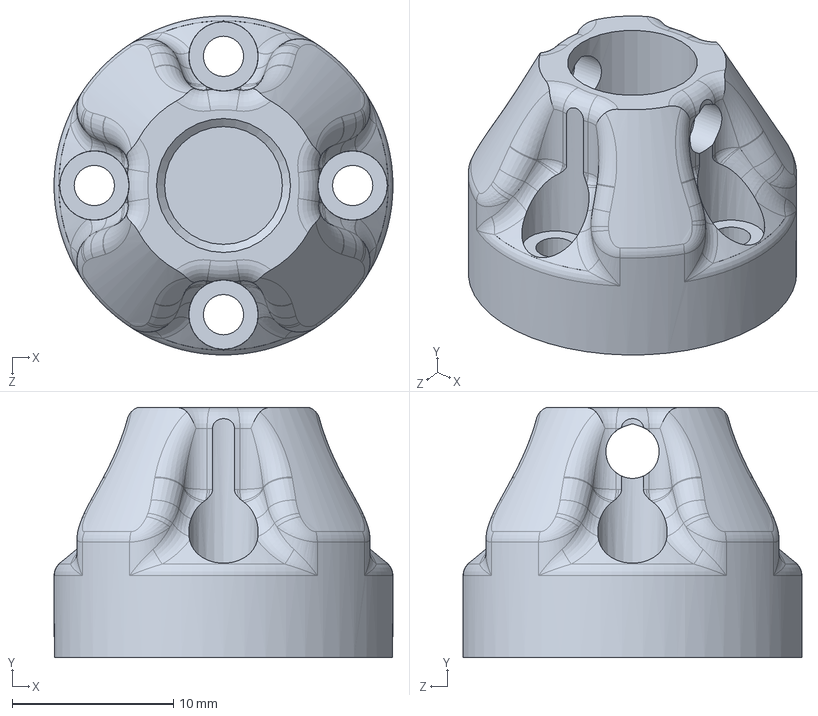
[picture p69: CAD file, 2021-04-16]
Mechanical_Components/ASSY_SCARUS/ASSY_ROBOT/DYNAMIXEL_COUPLING.sldprt
21.0 x 15.5 x 21.0 mm
