ethanlefebv/S4H2021-Scarus/Mechanical_Components/ASSY_SCARUS/ASSY_SLIDE/DOVETAIL_SPACER.SLDPRT

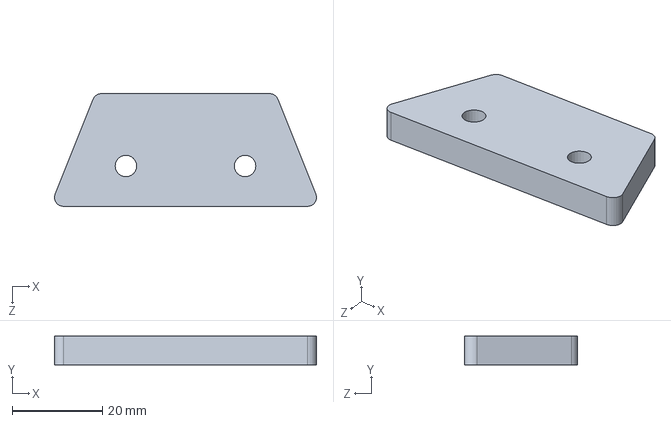
[picture p70: CAD file, 2021-04-16]
Mechanical_Components/ASSY_SCARUS/ASSY_SLIDE/DOVETAIL_SPACER.SLDPRT
58.1 x 6.35 x 25.0 mm
