ethanlefebv/S4H2021-Scarus/Mechanical_Components/DXF/SLIDE/SLIDE_LOCK_CAM_SUPPORT.DXF

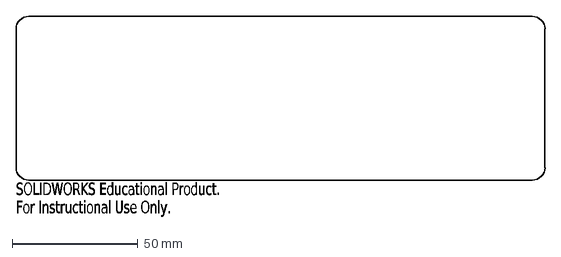
[picture p71: CAD file, 2021-04-16]
Mechanical_Components/DXF/SLIDE/SLIDE_LOCK_CAM_SUPPORT.DXF
SOLIDWORKS Educational Product.
For Instructional Use Only.
