ethanlefebv/S4H2021-Scarus/Mechanical_Components/ASSY_SCARUS/ASSY_SLIDE/PLA_BOT_SLIDE.SLDPRT

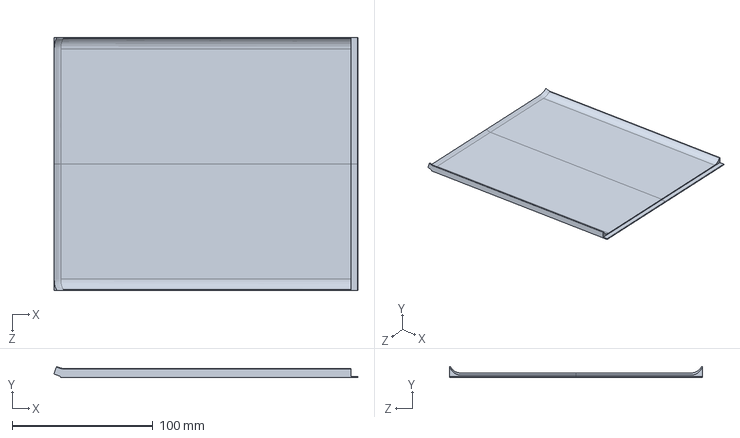
[picture p72: CAD file, 2021-04-16]
Mechanical_Components/ASSY_SCARUS/ASSY_SLIDE/PLA_BOT_SLIDE.SLDPRT
216.3 x 7.74 x 180.0 mm
