ethanlefebv/S4H2021-Scarus/Mechanical_Components/ASSY_SCARUS/ASSY_ROBOT/ARM_SEGMENT_2.SLDPRT

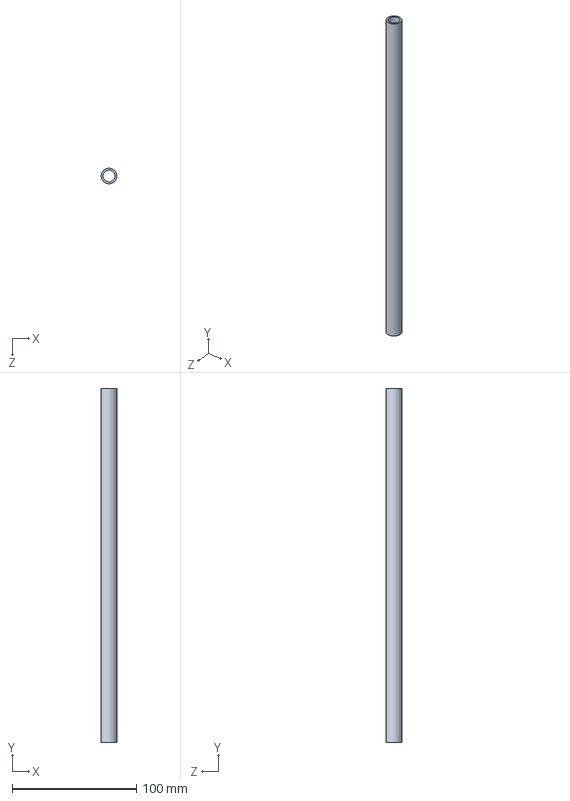
[picture p73: CAD file, 2021-04-16]
Mechanical_Components/ASSY_SCARUS/ASSY_ROBOT/ARM_SEGMENT_2.SLDPRT
12.7 x 285.0 x 12.7 mm
