ethanlefebv/S4H2021-Scarus/Mechanical_Components/ASSY_SCARUS/ASSY_ROBOT/MOTOR_JOINT_V2.SLDPRT

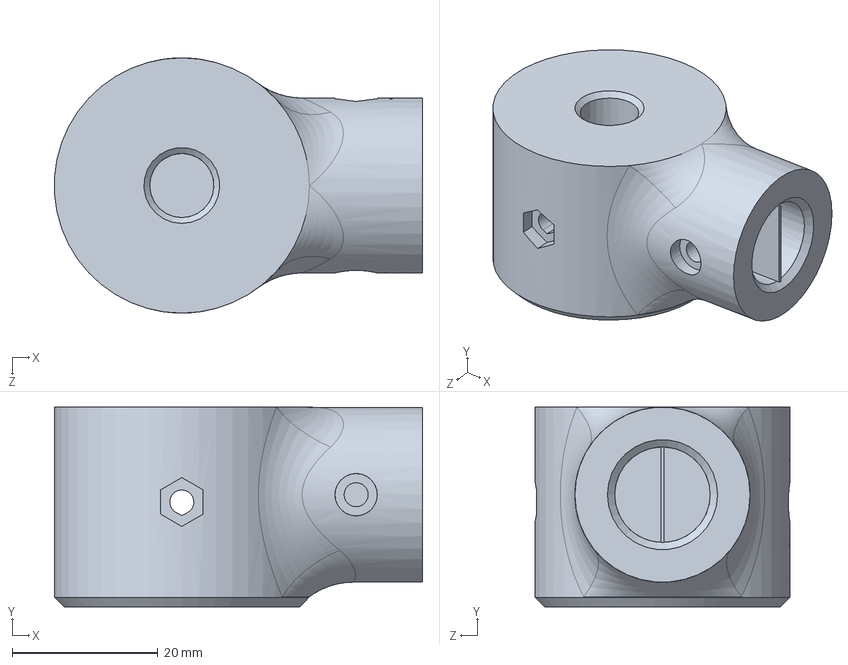
[picture p74: CAD file, 2021-04-16]
Mechanical_Components/ASSY_SCARUS/ASSY_ROBOT/MOTOR_JOINT_V2.SLDPRT
50.5 x 27.4 x 35.0 mm
