ethanlefebv/S4H2021-Scarus/Mechanical_Components/ASSY_SCARUS/ASSY_SLIDE/SUPPORT_SIDE_WALL.SLDPRT

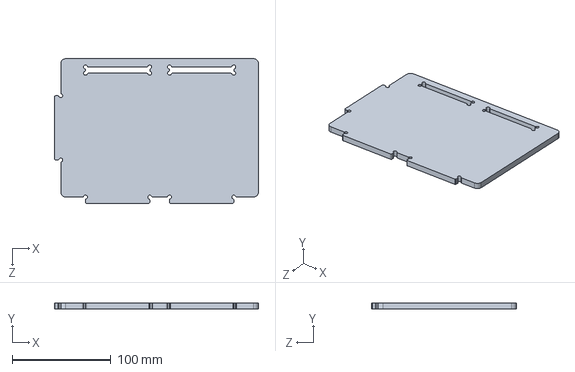
[picture p75: CAD file, 2021-04-16]
Mechanical_Components/ASSY_SCARUS/ASSY_SLIDE/SUPPORT_SIDE_WALL.SLDPRT
206.4 x 6.35 x 146.4 mm
