ethanlefebv/S4H2021-Scarus/Mechanical_Components/ASSY_SCARUS/ASSY_ROBOT/5_16_THREADED_ROD.SLDPRT

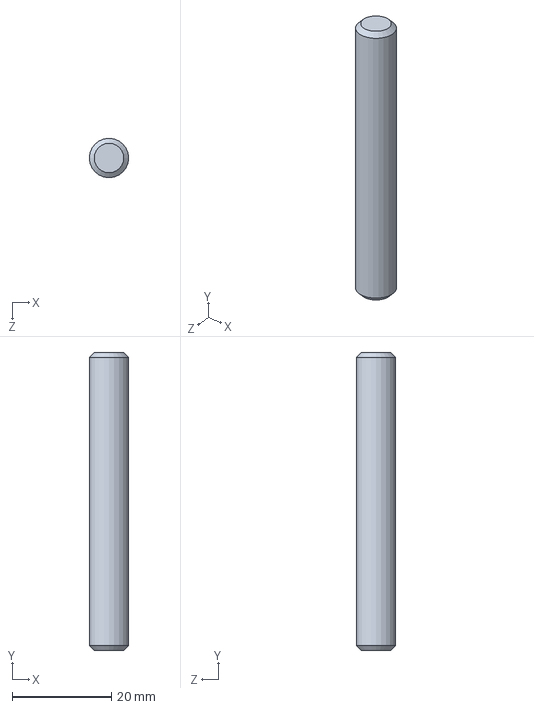
[picture p76: CAD file, 2021-04-16]
Mechanical_Components/ASSY_SCARUS/ASSY_ROBOT/5_16_THREADED_ROD.SLDPRT
7.94 x 60.0 x 7.94 mm
