ethanlefebv/S4H2021-Scarus/Mechanical_Components/ASSY_SCARUS/ASSY_SLIDE/SUPPORT_SLIDING_BOARD_SUPPORT.SLDPRT

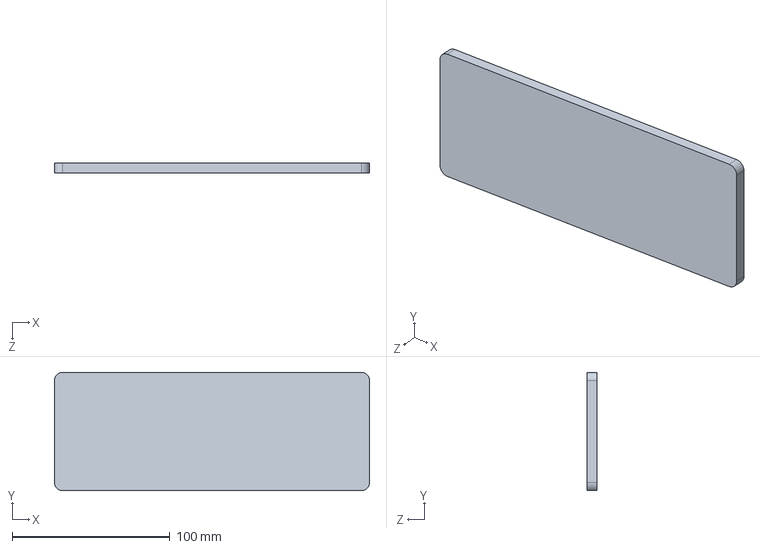
[picture p77: CAD file, 2021-04-16]
Mechanical_Components/ASSY_SCARUS/ASSY_SLIDE/SUPPORT_SLIDING_BOARD_SUPPORT.SLDPRT
200.0 x 75.0 x 6.35 mm
