ethanlefebv/S4H2021-Scarus/Mechanical_Components/ASSY_SCARUS/ASSY_SLIDE/PLA_TOP_SLIDE.SLDPRT

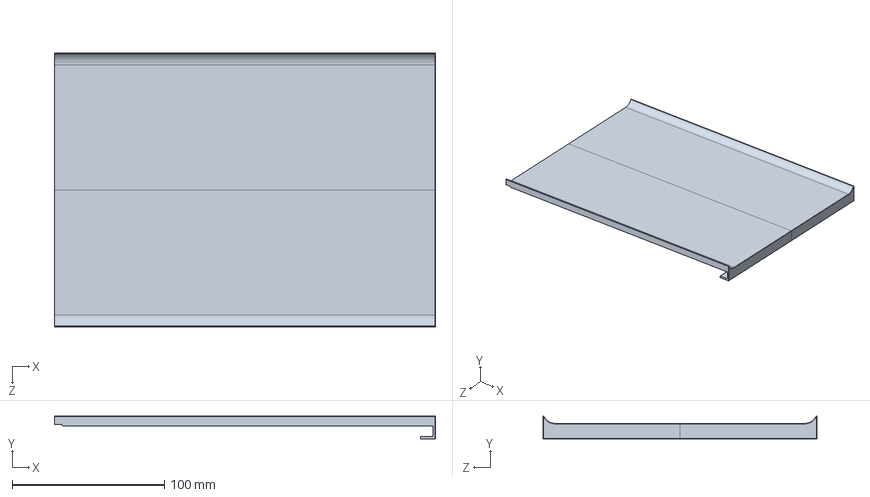
[picture p78: CAD file, 2021-04-16]
Mechanical_Components/ASSY_SCARUS/ASSY_SLIDE/PLA_TOP_SLIDE.SLDPRT
250.0 x 15.0 x 180.0 mm
