ethanlefebv/S4H2021-Scarus/Mechanical_Components/ASSY_SCARUS/ASSY_SLIDE/SIDE_WALL.SLDPRT

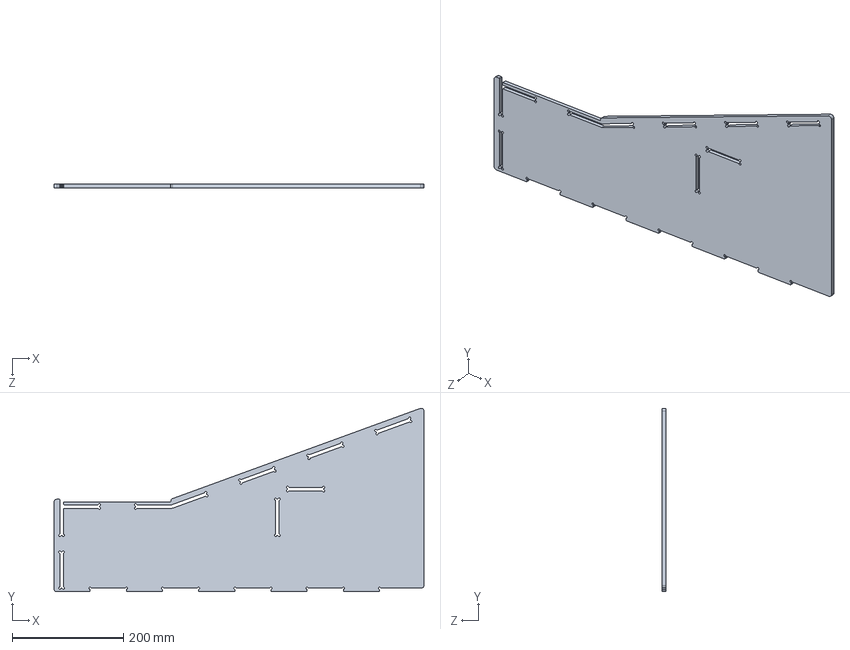
[picture p79: CAD file, 2021-04-16]
Mechanical_Components/ASSY_SCARUS/ASSY_SLIDE/SIDE_WALL.SLDPRT
665.0 x 329.8 x 6.35 mm
