ethanlefebv/S4H2021-Scarus/Mechanical_Components/ASSY_SCARUS/ASSY_SLIDE/SUPPORT_FRONT_WALL.SLDPRT

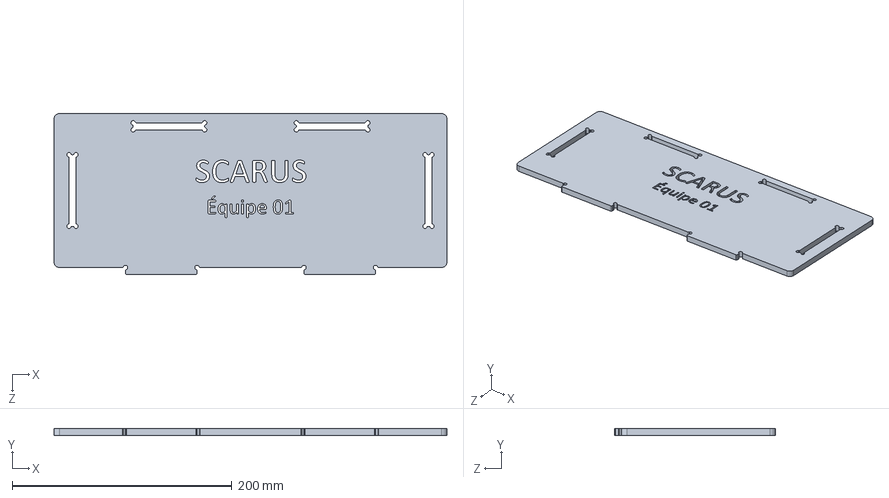
[picture p80: CAD file, 2021-04-16]
Mechanical_Components/ASSY_SCARUS/ASSY_SLIDE/SUPPORT_FRONT_WALL.SLDPRT
357.3 x 6.35 x 146.4 mm
