ethanlefebv/S4H2021-Scarus/Mechanical_Components/ASSY_SCARUS/ASSY_SLIDE/BUCKET.SLDPRT

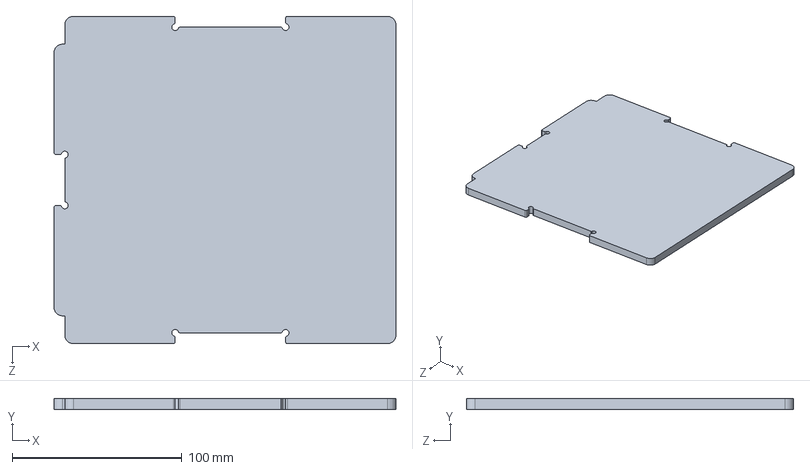
[picture p81: CAD file, 2021-04-16]
Mechanical_Components/ASSY_SCARUS/ASSY_SLIDE/BUCKET.SLDPRT
201.3 x 6.35 x 192.7 mm
