ethanlefebv/S4H2021-Scarus/Mechanical_Components/ASSY_SCARUS/ASSY_SLIDE/PLA_BUCKET.SLDPRT

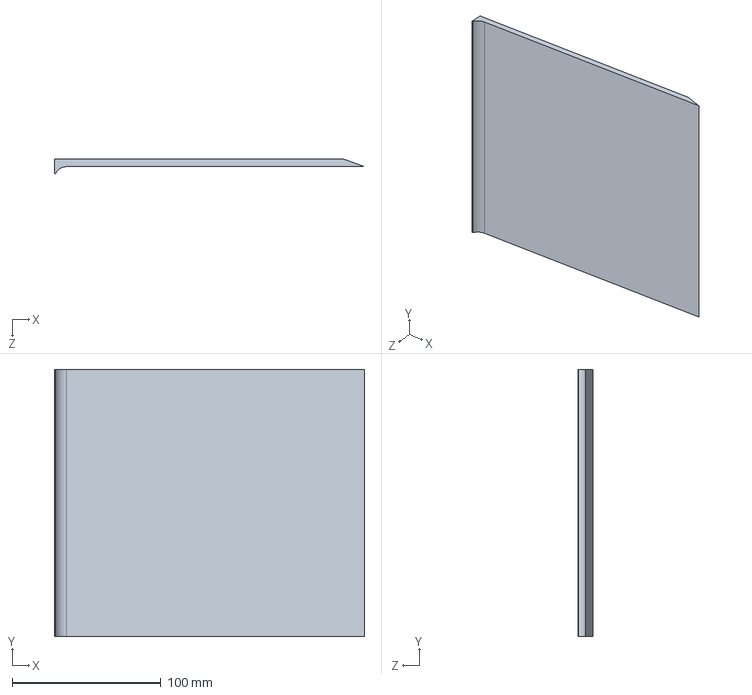
[picture p82: CAD file, 2021-04-16]
Mechanical_Components/ASSY_SCARUS/ASSY_SLIDE/PLA_BUCKET.SLDPRT
208.7 x 180.0 x 9.82 mm
