ethanlefebv/S4H2021-Scarus/Mechanical_Components/ASSY_SCARUS/ASSY_SLIDE/SUPPORT_TOP_BOARD.SLDPRT

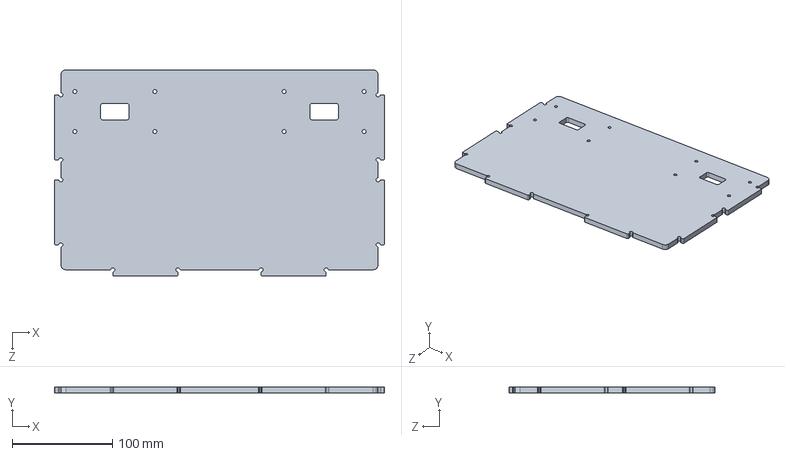
[picture p83: CAD file, 2021-04-16]
Mechanical_Components/ASSY_SCARUS/ASSY_SLIDE/SUPPORT_TOP_BOARD.SLDPRT
330.0 x 6.35 x 206.4 mm
