ethanlefebv/S4H2021-Scarus/Mechanical_Components/ASSY_SCARUS/ASSY_SLIDE/FRONT_WALL.SLDPRT

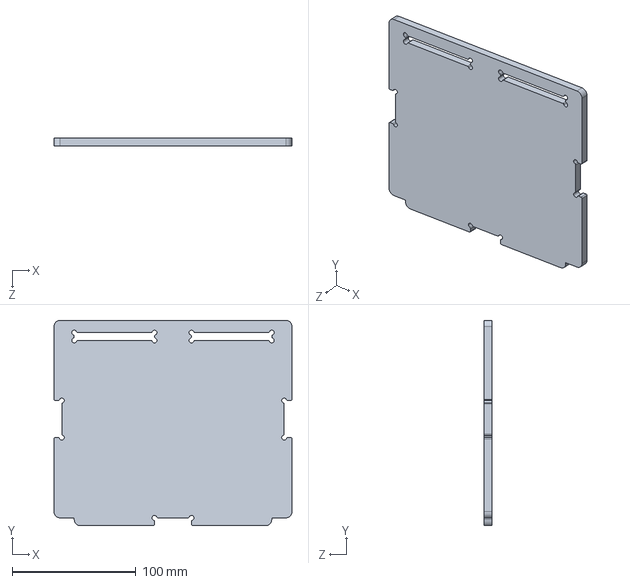
[picture p84: CAD file, 2021-04-16]
Mechanical_Components/ASSY_SCARUS/ASSY_SLIDE/FRONT_WALL.SLDPRT
192.7 x 166.3 x 6.35 mm
