ethanlefebv/S4H2021-Scarus/Mechanical_Components/ASSY_SCARUS/ASSY_SLIDE/BASE.SLDPRT

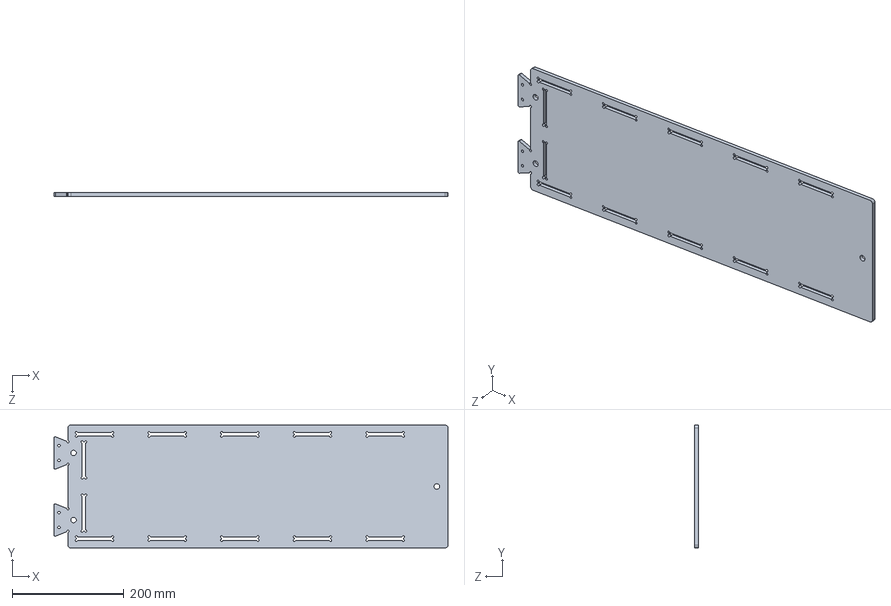
[picture p85: CAD file, 2021-04-16]
Mechanical_Components/ASSY_SCARUS/ASSY_SLIDE/BASE.SLDPRT
705.0 x 220.0 x 6.35 mm
