ethanlefebv/S4H2021-Scarus/init_stop/init_stop_sequences.py

from Communication.serial_functions.functions import *
import cv2
import time
import argparse
import serial

def init_sequence():
    """Initialize the system.

    Read the arguments provided to the program.
    Initialize the camera.
    Initialize the communication.
    Start the main program on the OpenCR.
    """
    baudrate = 115200
    camera_index, port = init_args()
    cam = init_camera(camera_index)
    ser = init_comm(port, baudrate)
    init_opencr(ser)
    return cam, port, ser


def init_args():
    """Read the arguments provided to the program.
    """
    parser = argparse.ArgumentParser()
    parser.add_argument('-c', required=True, type=int, help='Index of the camera.')
    parser.add_argument('-p', required=True, help='Port used for serial communication.')
    args = parser.parse_args()
    camera_index = args.c
    port = args.p
    return camera_index, port


def init_camera(camera_index):
    """Initialize the camera.
    """
    camera = cv2.VideoCapture(camera_index)
    return camera


def init_comm(port, baudrate):
    """Initialize the communication with the wanted serial device.
    """
    print("Opening Serial communication with {0}.".format(port))
    ser = serial.Serial(port, baudrate)
    ser.flush()
    return ser


def init_opencr(ser):
    """Start the main program on the OpenCR.

    Verify if the OpenCR is currently sleeping, then send the START
    command.
    """
    msg = get_data(ser)
    # Confirm the OpenCR is waiting to start
    if msg != "Waiting for the START command.":
        raise SerialError("The OpenCR is not waiting to start. Try restarting it.")

    print_sent_data(send_data(ser, "START"))
    data = wait_for_data(ser, "Starting the program.")


def stop_sequence(cam, port, ser):
    """Stop all systems.

    Stop the main program on the OpenCR.
    Release the camera.
    Close the communication with the serial device.
    """
    print_sent_data(send_data(ser, "STOP"))
    print_received_data(get_data(ser))

    cam.release()
    print("Closing Serial communication with {0}.".format(port))
    ser.close()
